dariusz-majchrzak/Meritum-1/docs/scans/1/cpu-mem.png

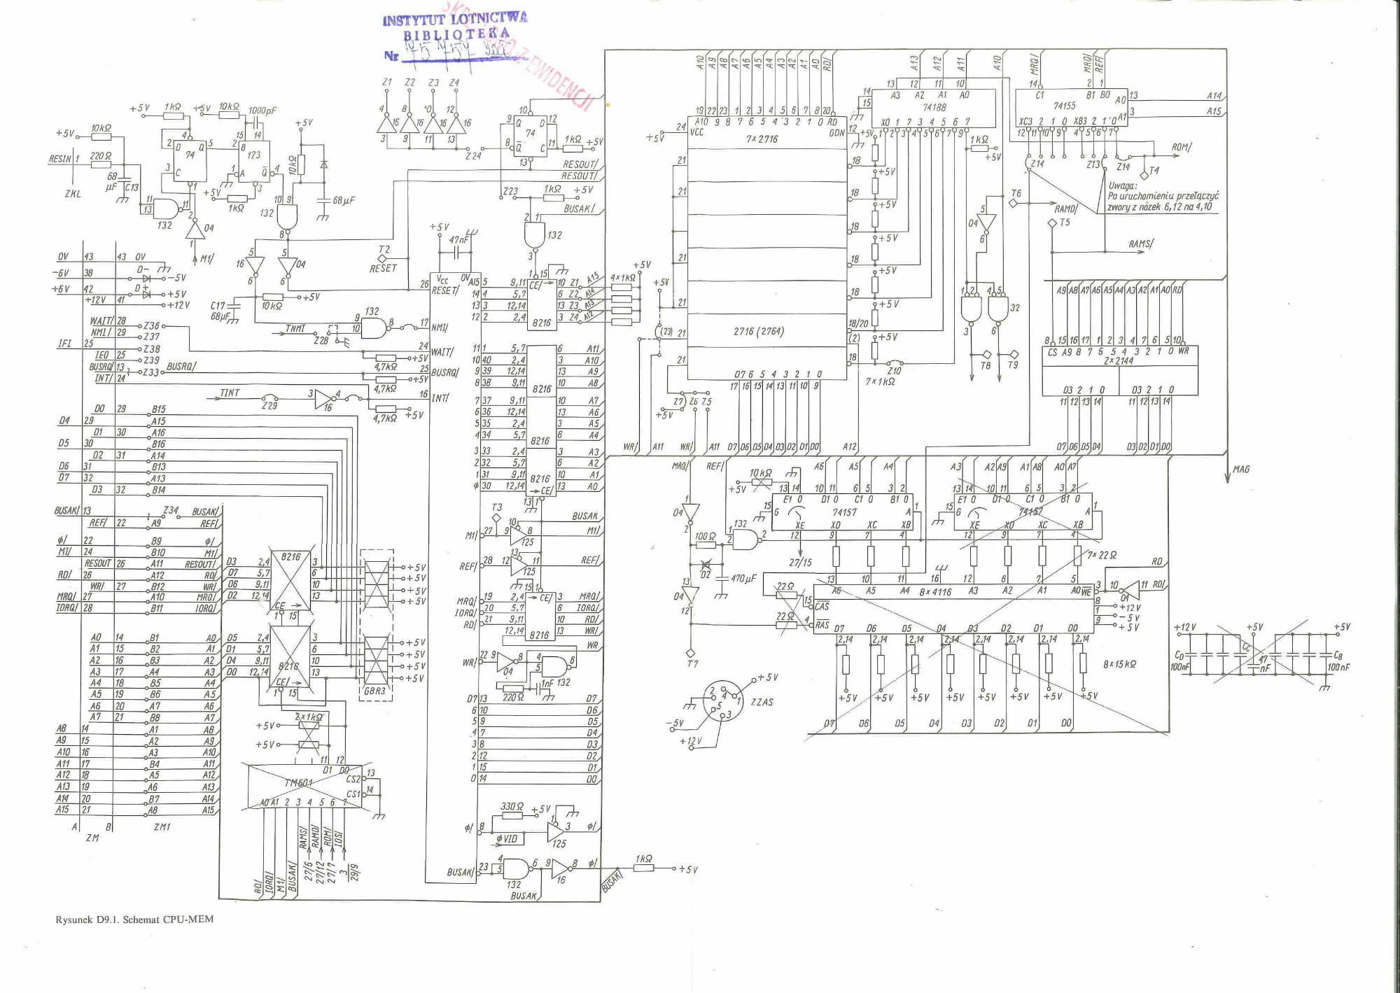
docs/scans/1/cpu-mem.png
