dariusz-majchrzak/Meritum-1/docs/scans/1/keyboard-1.png

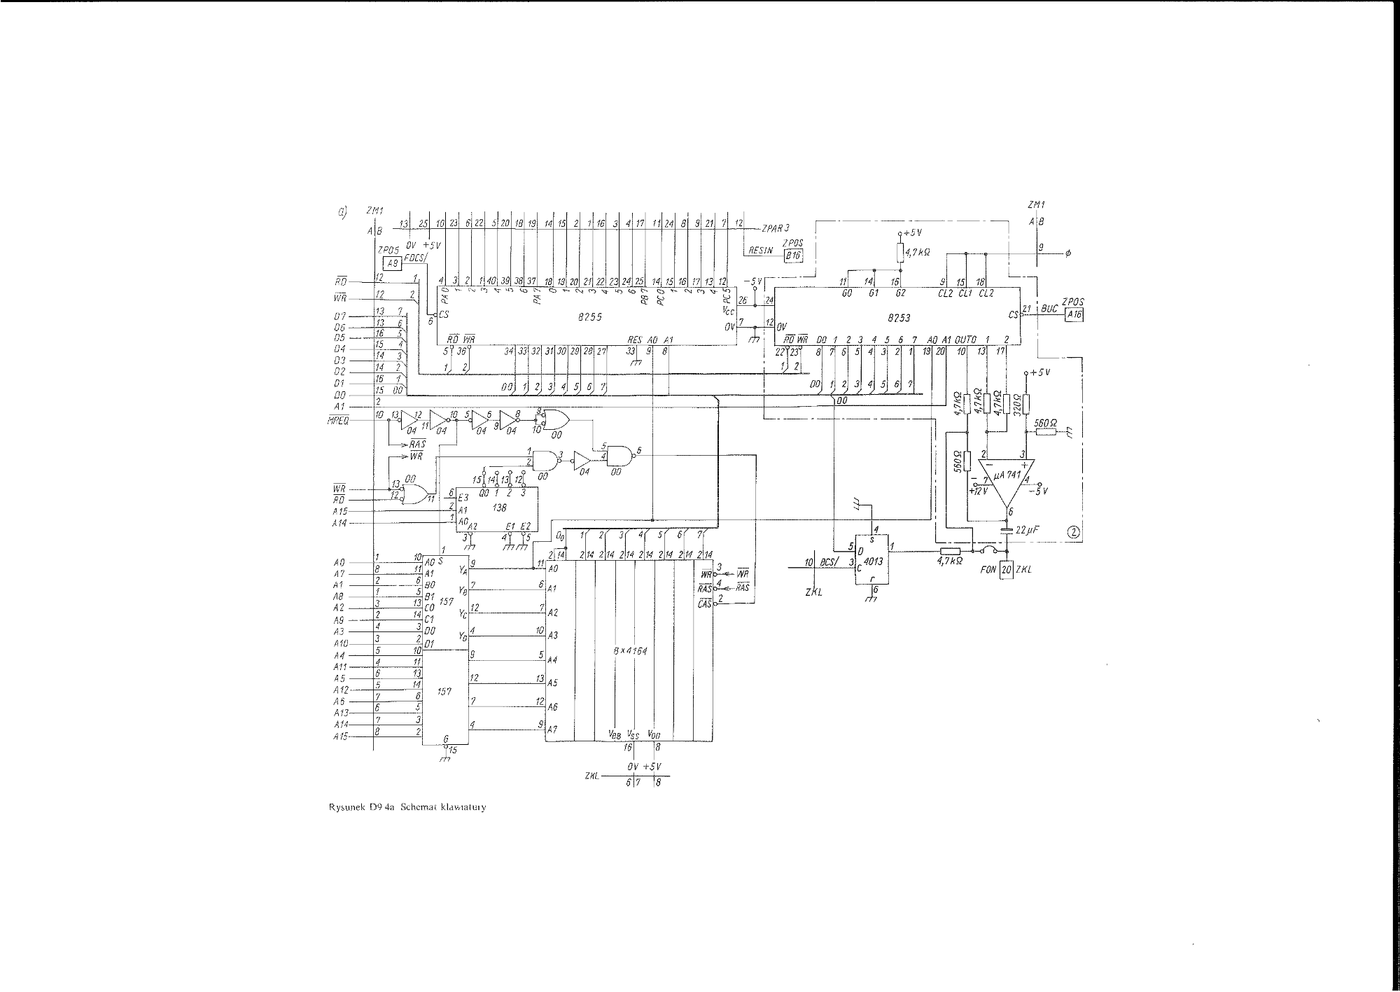
docs/scans/1/keyboard-1.png
