dariusz-majchrzak/Meritum-1/docs/scans/1/keyboard-2.png

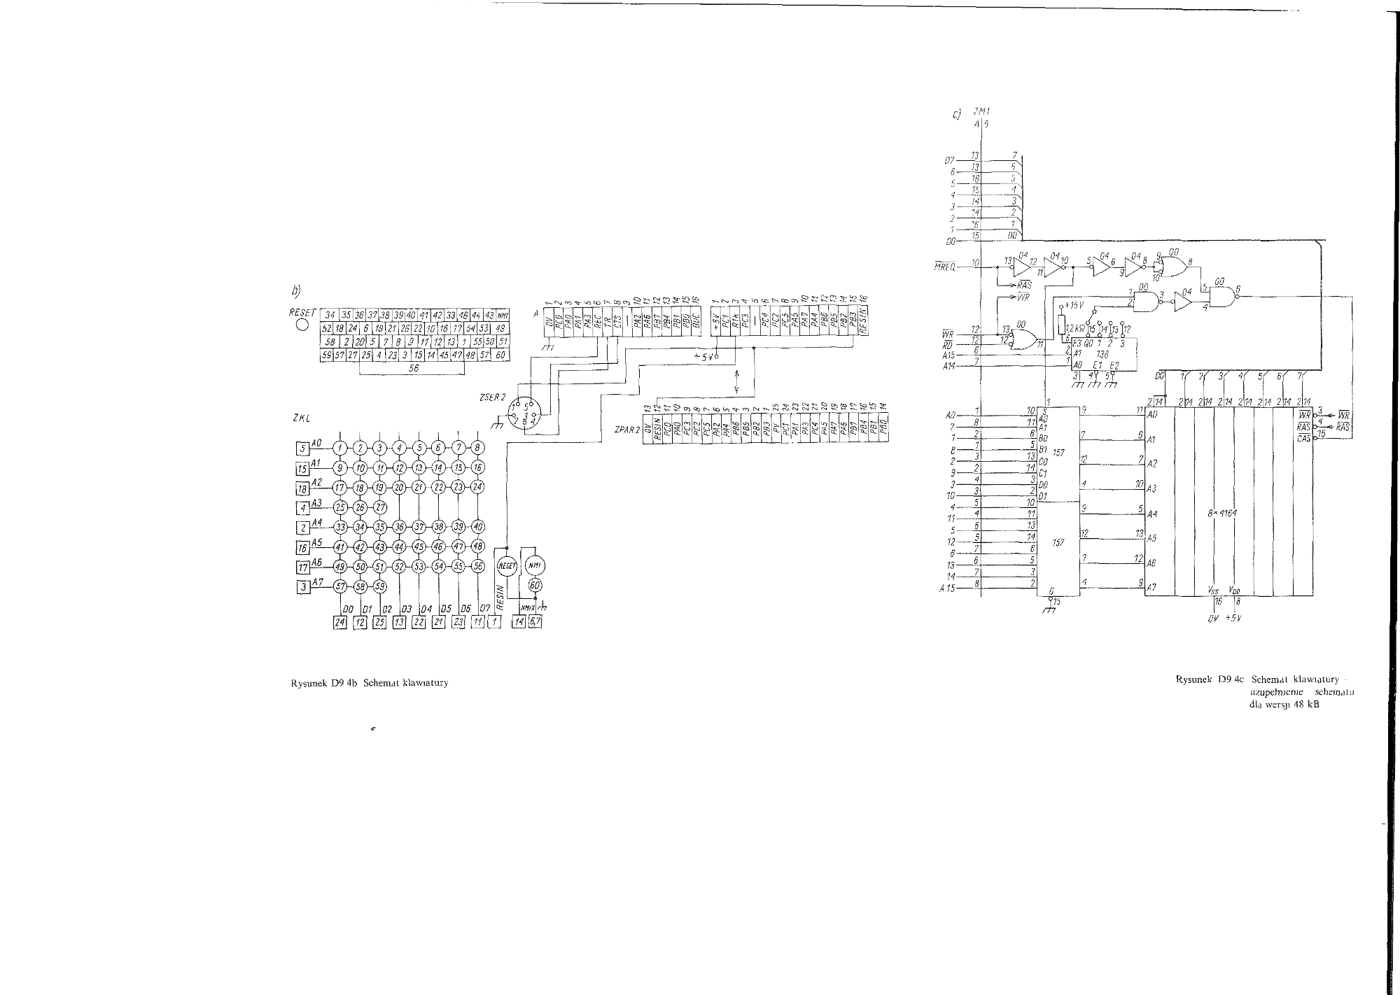
docs/scans/1/keyboard-2.png
