dariusz-majchrzak/Meritum-1/docs/scans/2/001.jpg

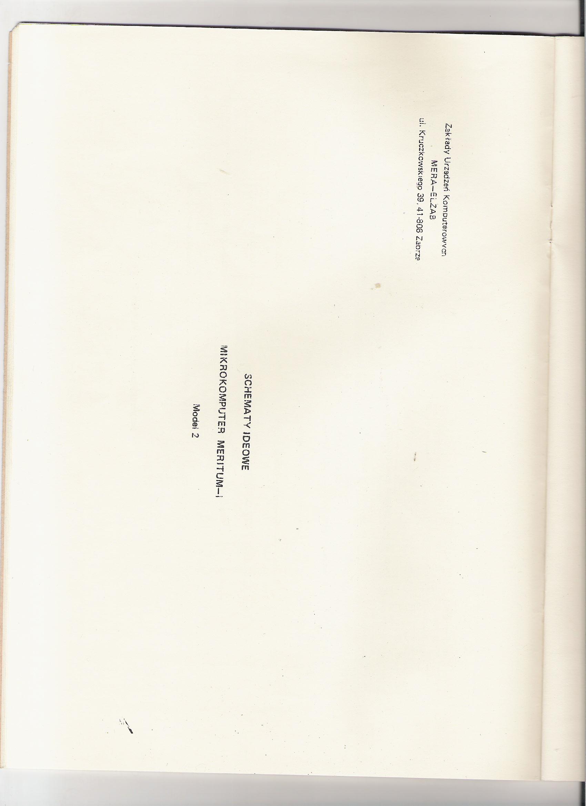
docs/scans/2/001.jpg
