dariusz-majchrzak/Meritum-1/docs/scans/2/002.jpg

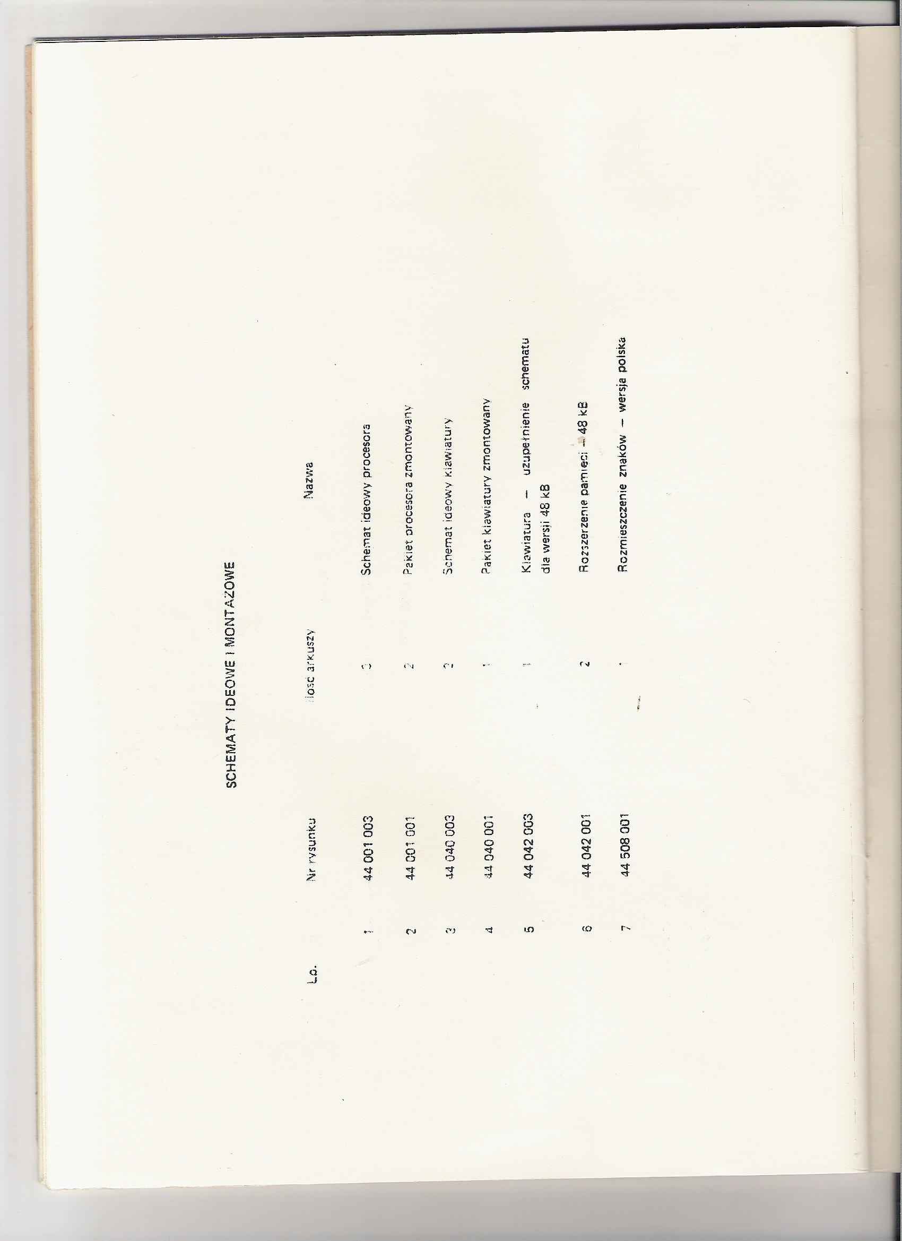
docs/scans/2/002.jpg
