dariusz-majchrzak/Meritum-1/docs/scans/2/003.jpg

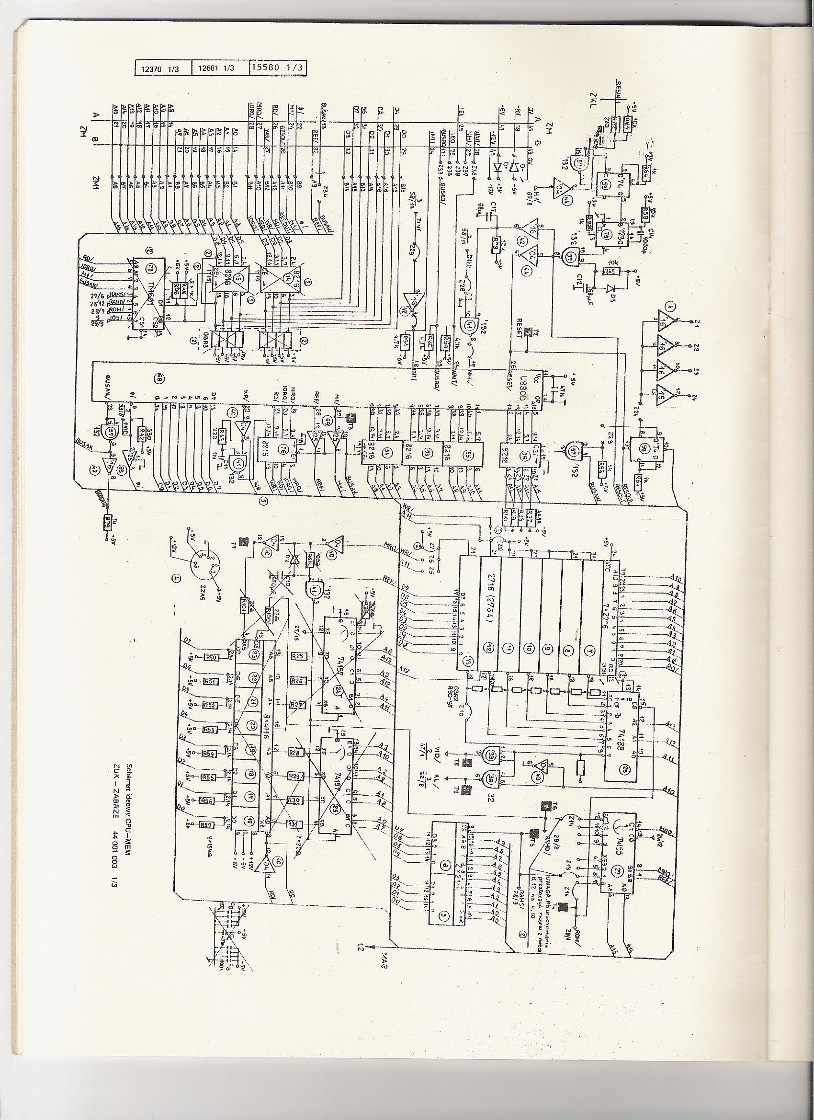
docs/scans/2/003.jpg
