dariusz-majchrzak/Meritum-1/docs/scans/2/004.jpg

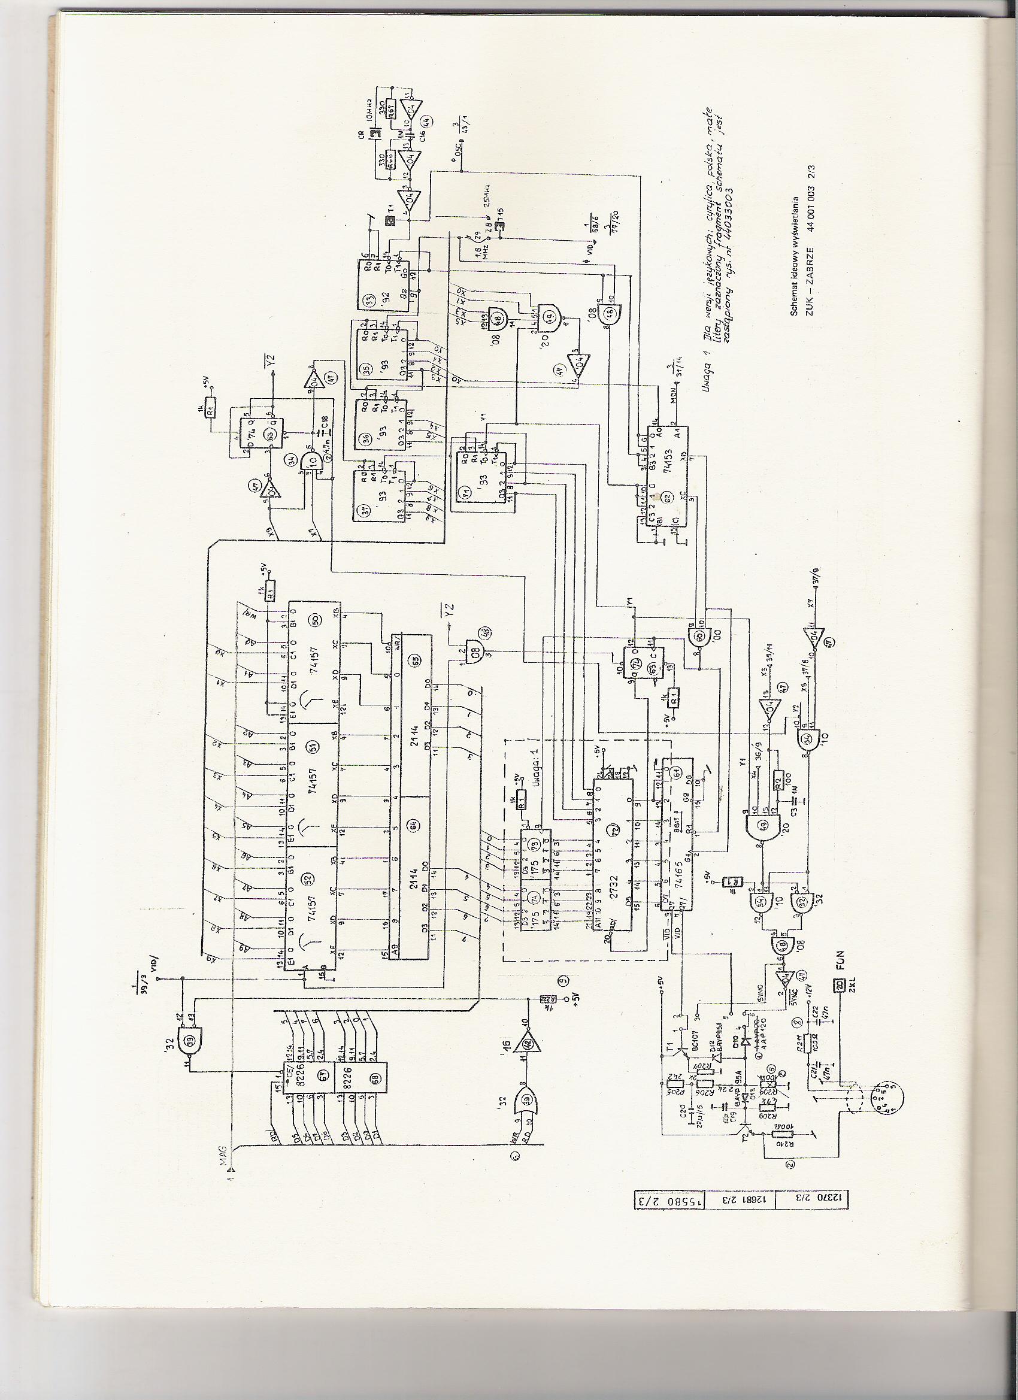
docs/scans/2/004.jpg
