dariusz-majchrzak/Meritum-1/docs/scans/2/005.jpg

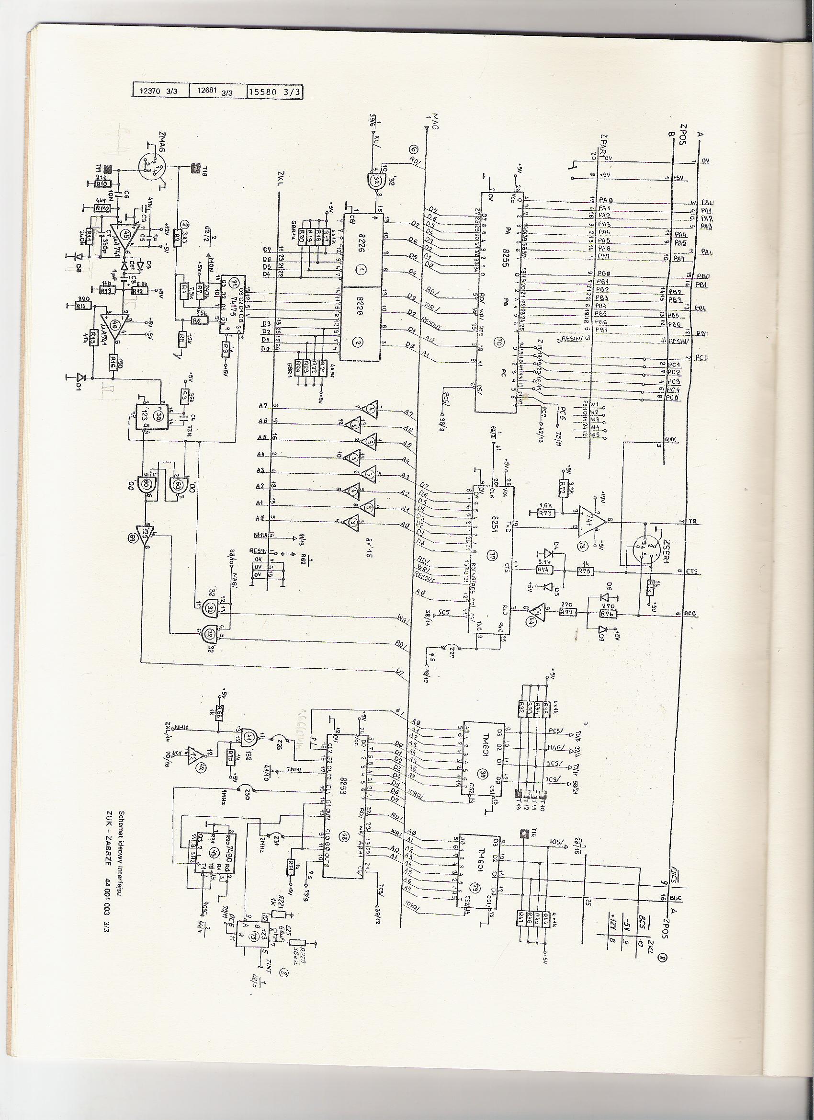
docs/scans/2/005.jpg
