dariusz-majchrzak/Meritum-1/docs/scans/2/006.jpg

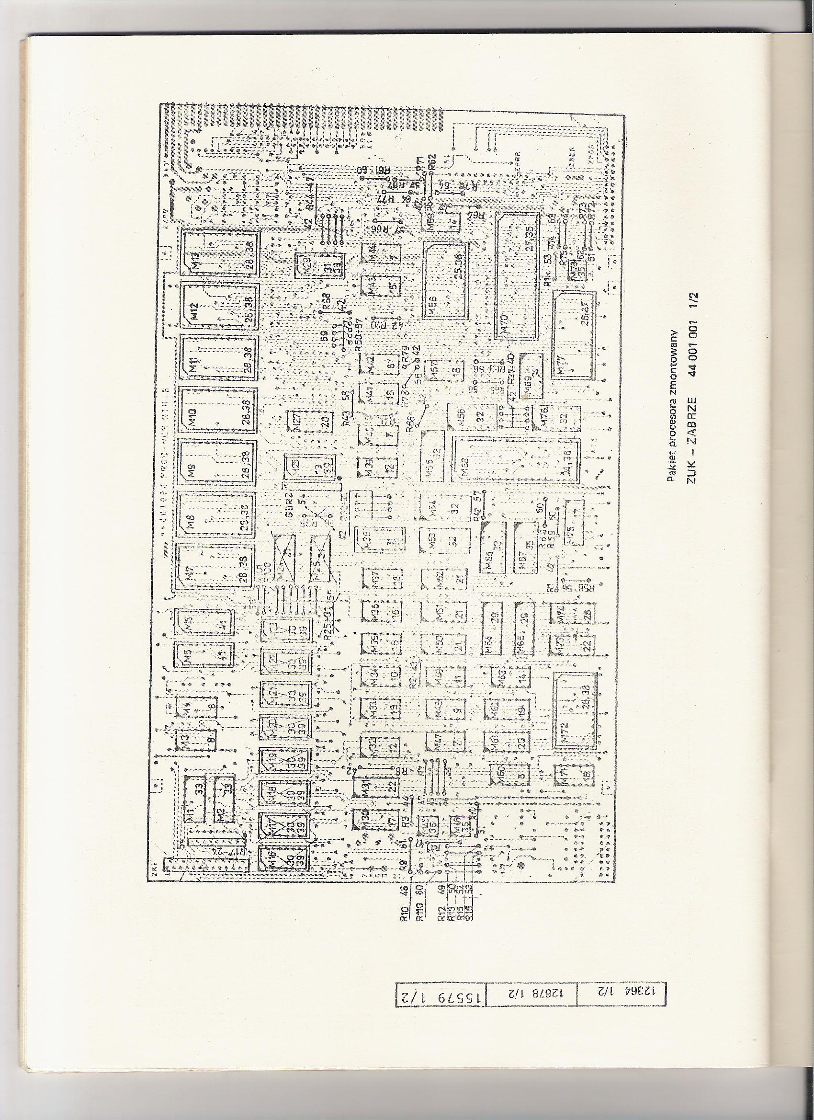
docs/scans/2/006.jpg
