dariusz-majchrzak/Meritum-1/docs/scans/2/007.jpg

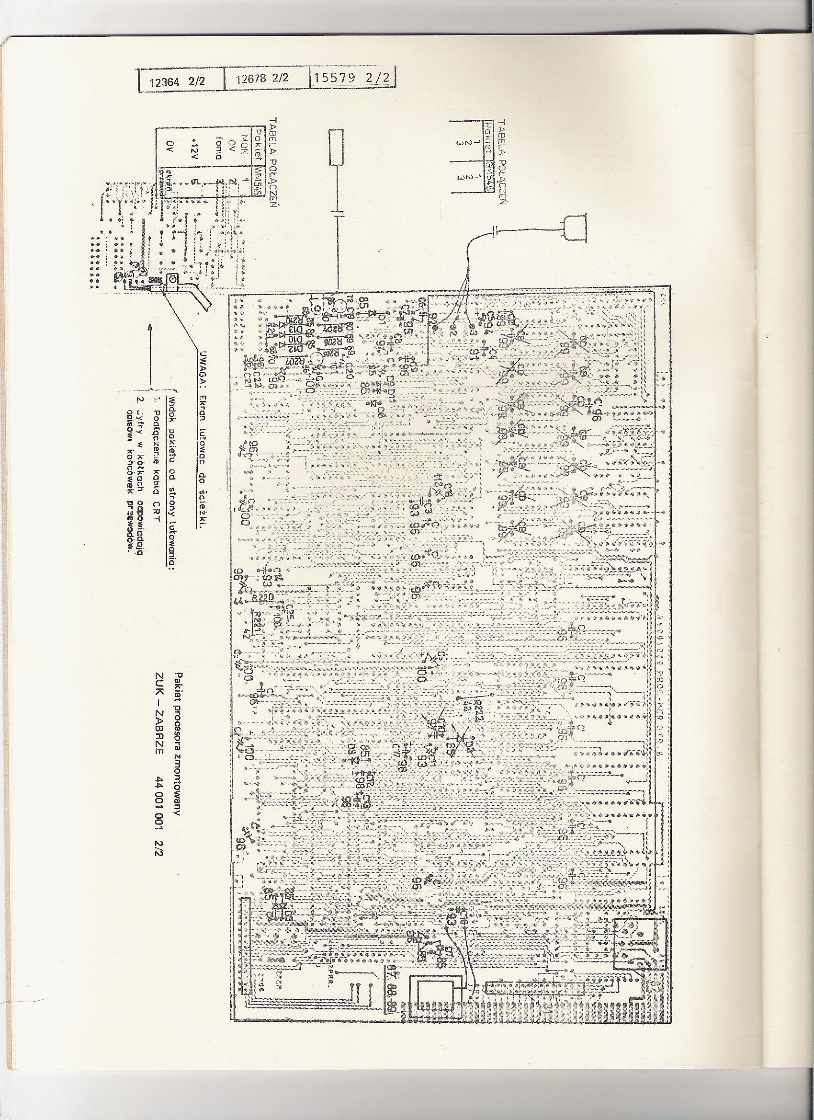
docs/scans/2/007.jpg
