dariusz-majchrzak/Meritum-1/docs/scans/2/008.jpg

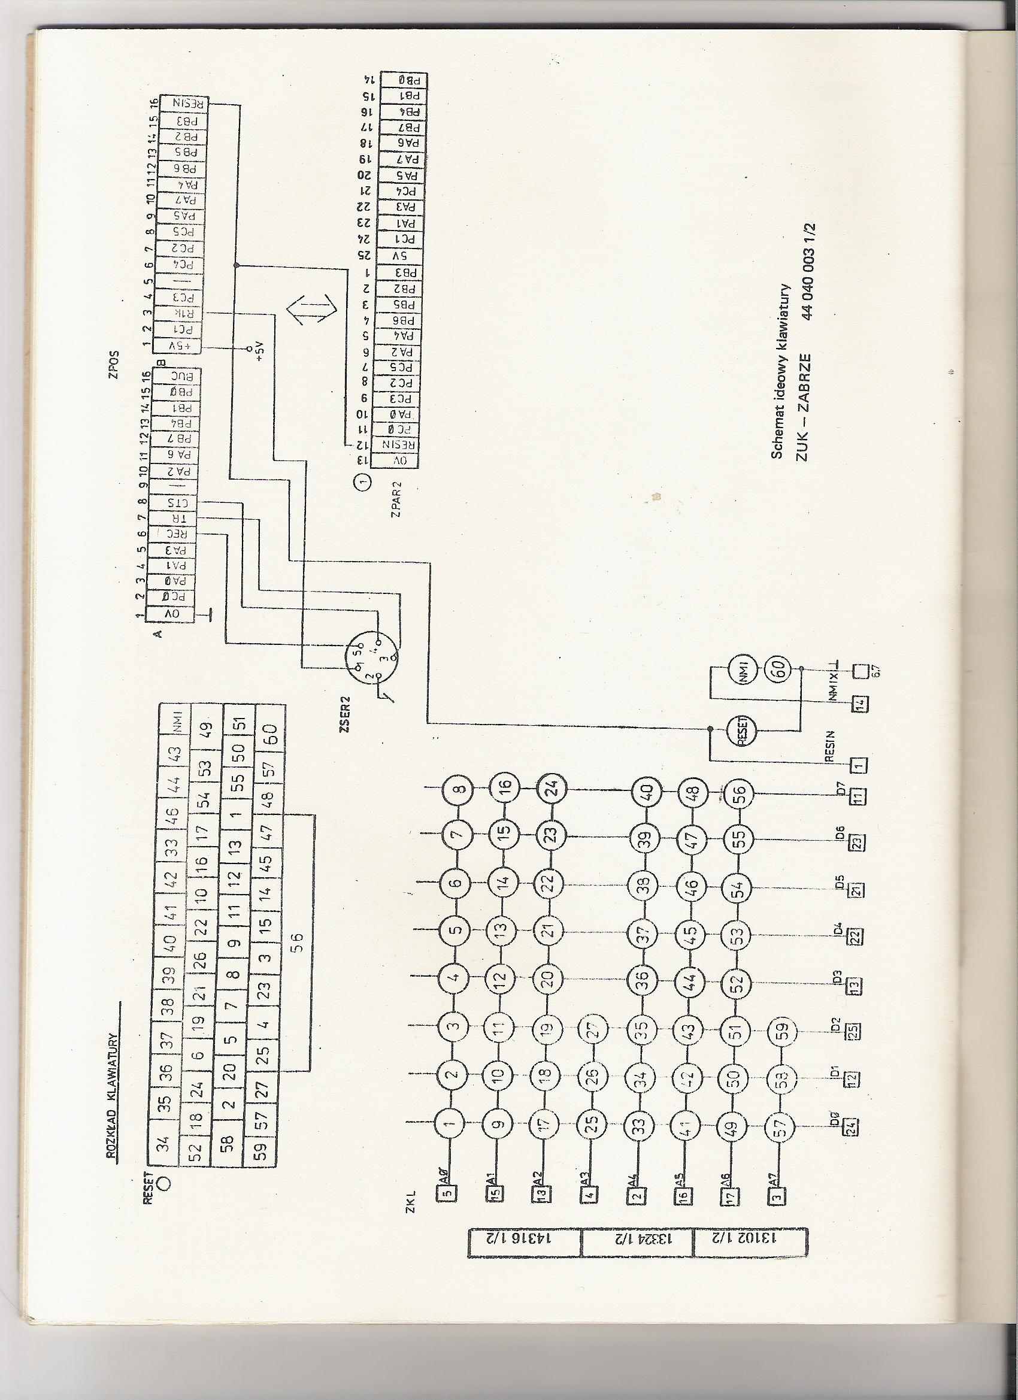
docs/scans/2/008.jpg
