dariusz-majchrzak/Meritum-1/docs/scans/2/009.jpg

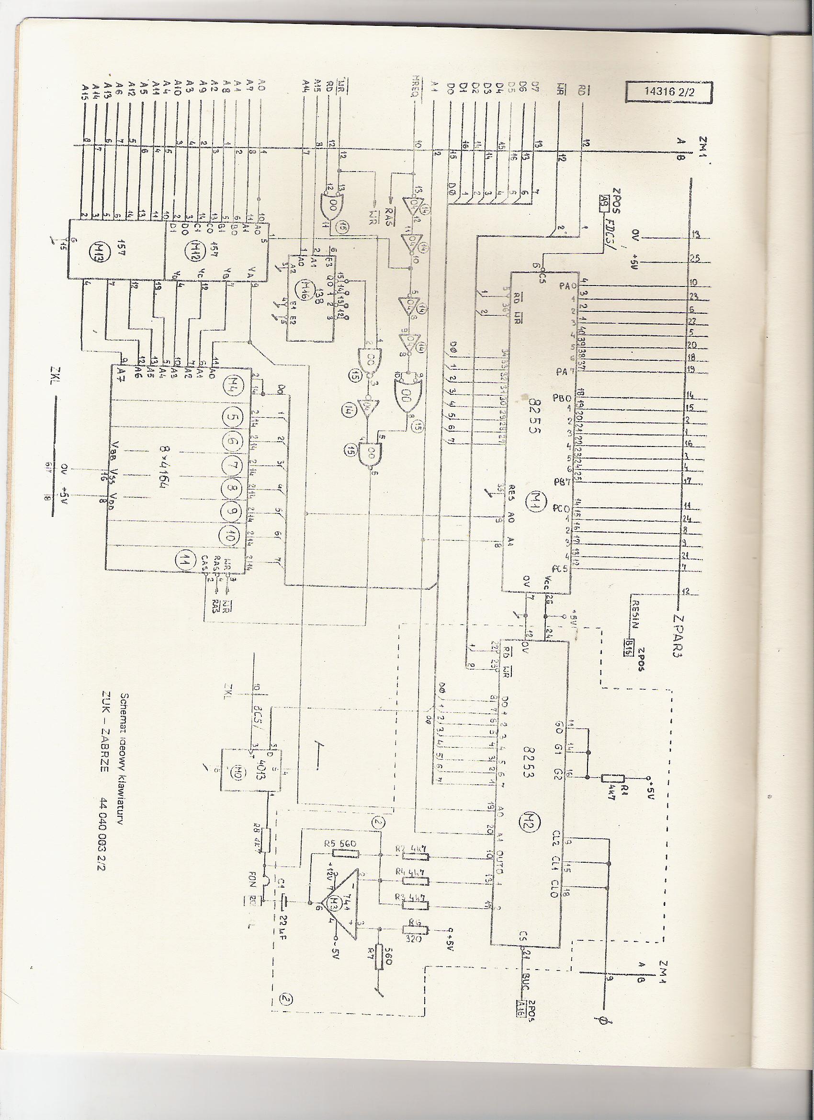
docs/scans/2/009.jpg
