dariusz-majchrzak/Meritum-1/docs/scans/2/010.jpg

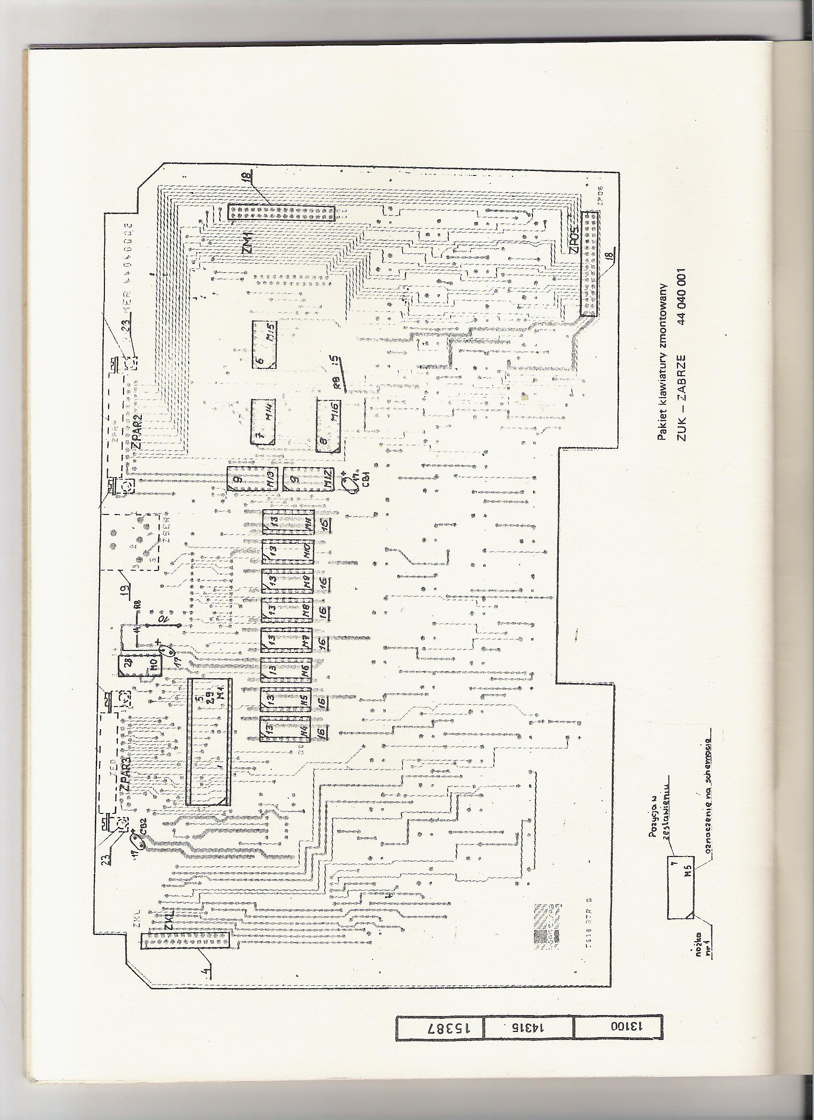
docs/scans/2/010.jpg
