dariusz-majchrzak/Meritum-1/docs/scans/2/011.jpg

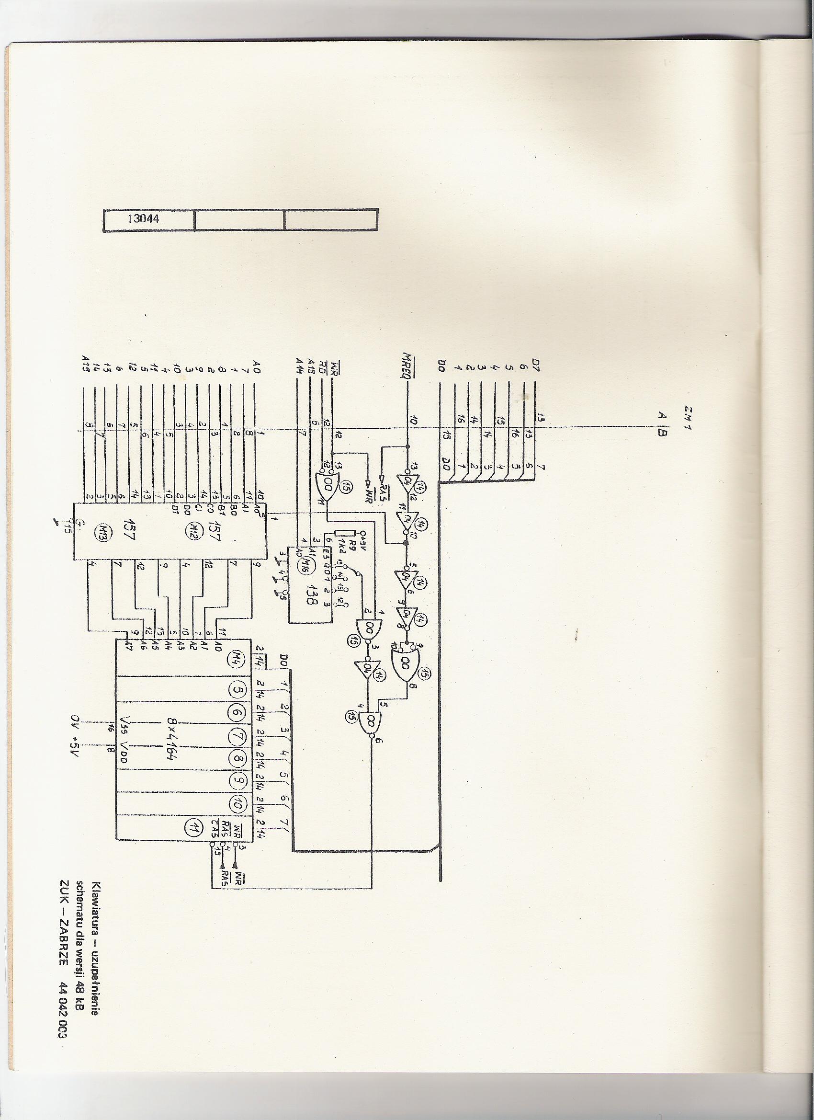
docs/scans/2/011.jpg
