dariusz-majchrzak/Meritum-1/docs/scans/2/012.jpg

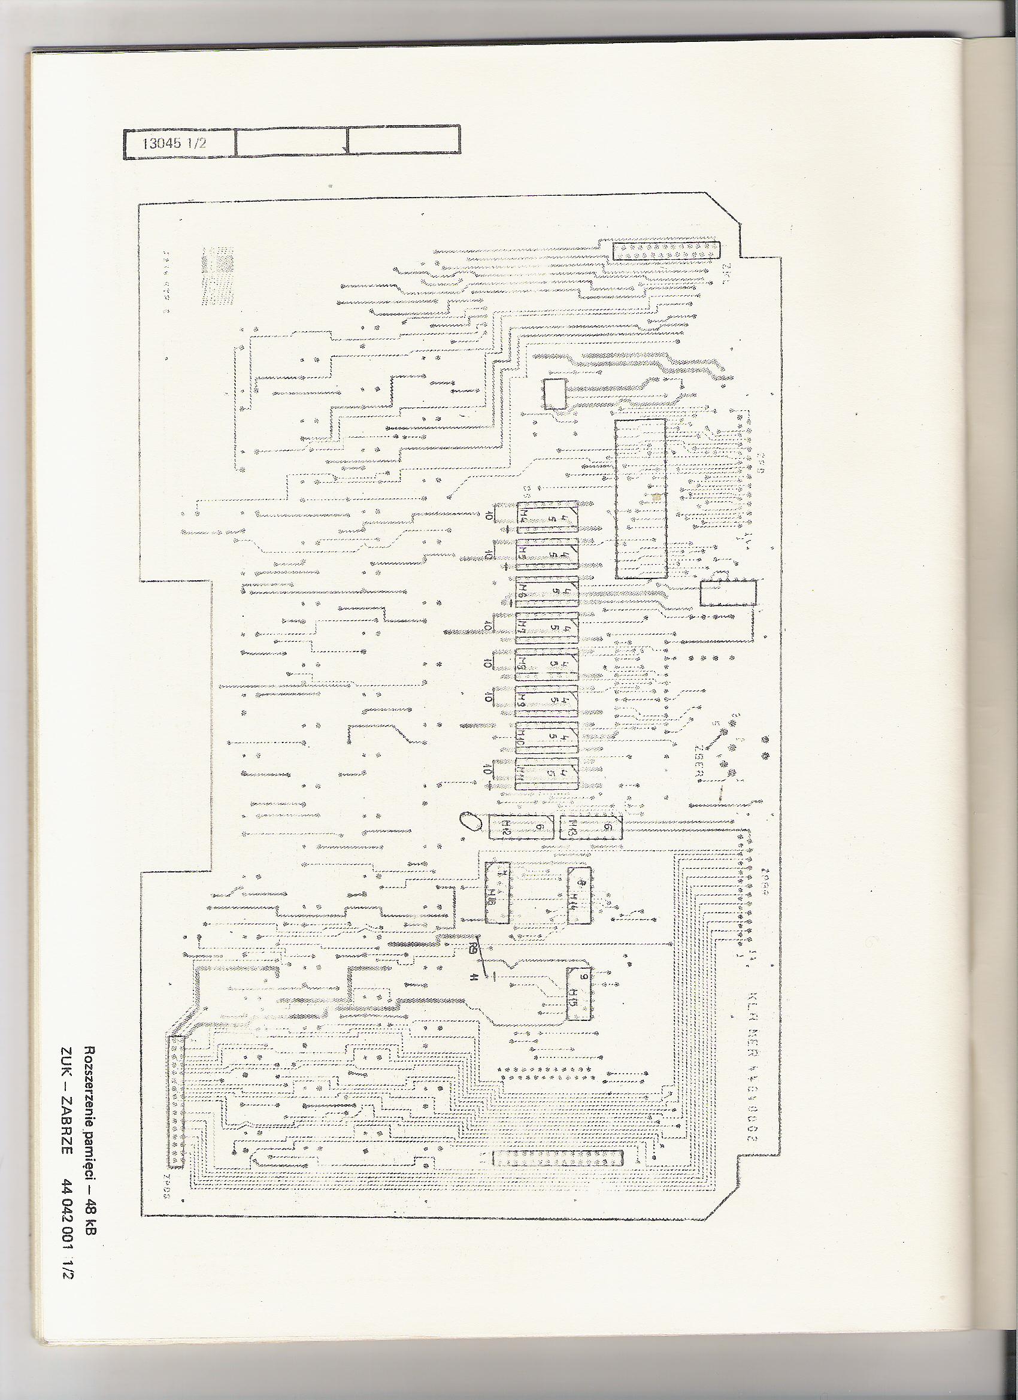
docs/scans/2/012.jpg
