dariusz-majchrzak/Meritum-1/docs/scans/2/013.jpg

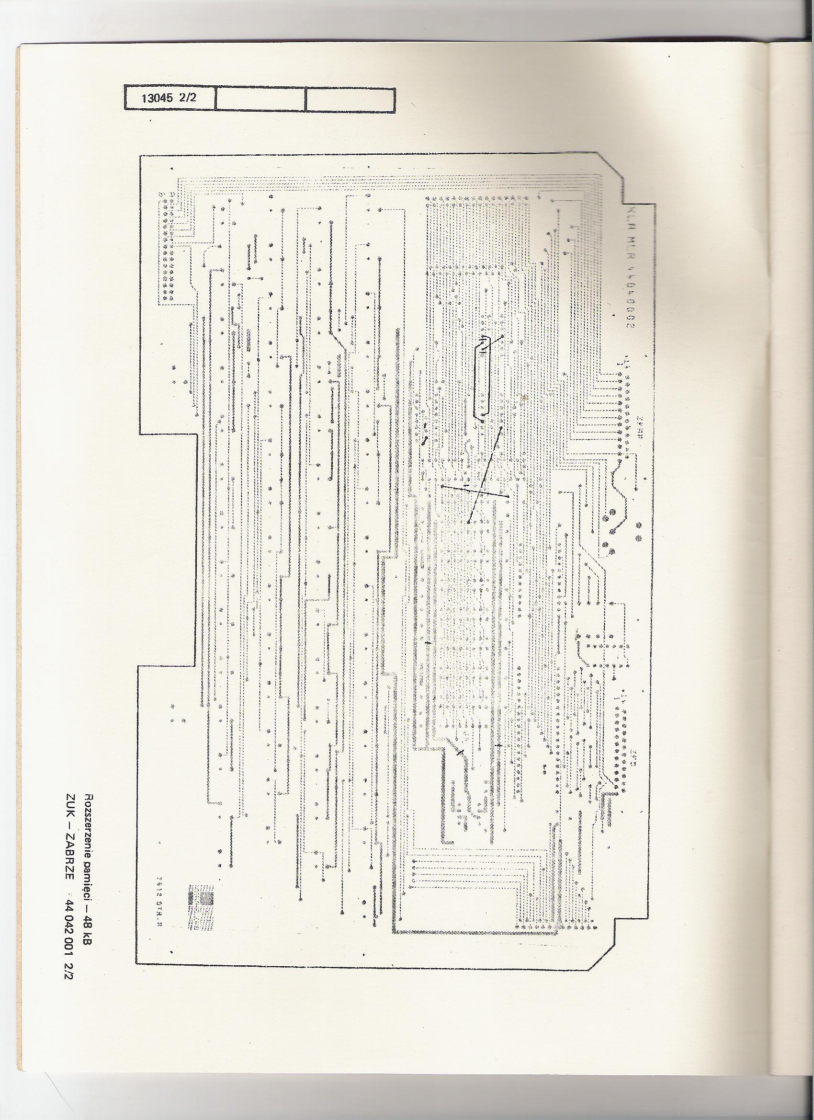
docs/scans/2/013.jpg
