dariusz-majchrzak/Meritum-1/docs/scans/2/014.jpg

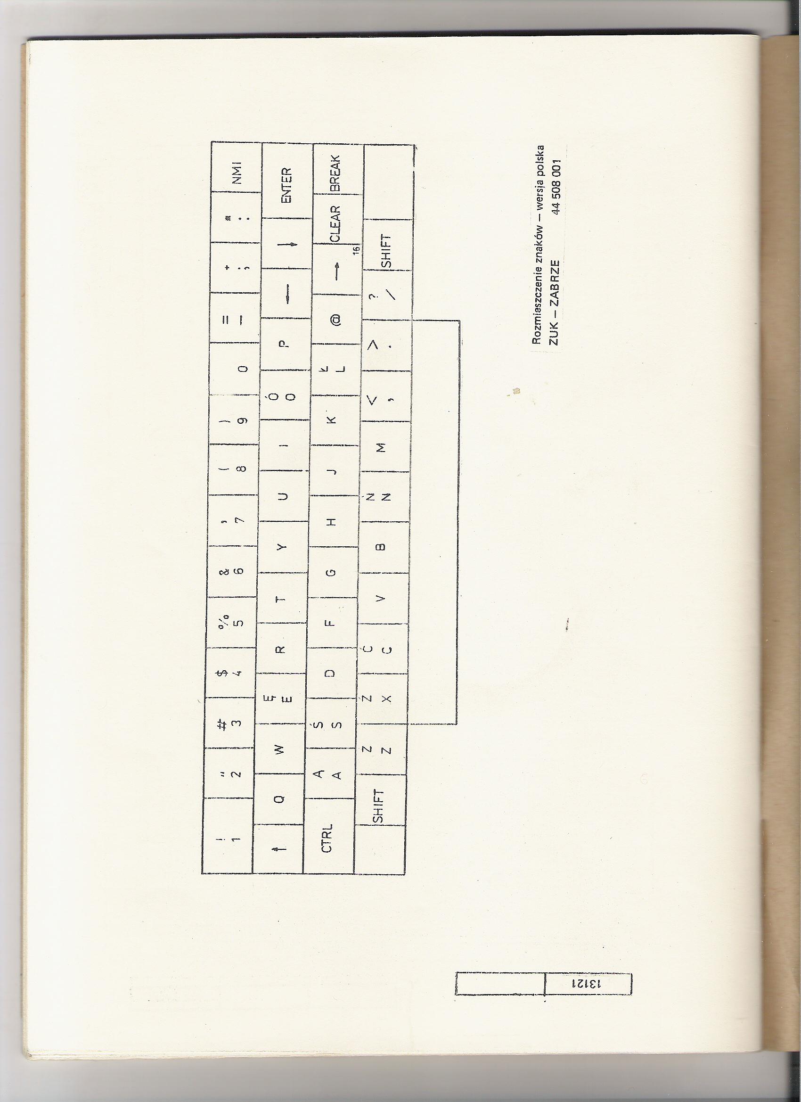
docs/scans/2/014.jpg
