dariusz-majchrzak/Meritum-1/docs/scans/3/D9-2.png

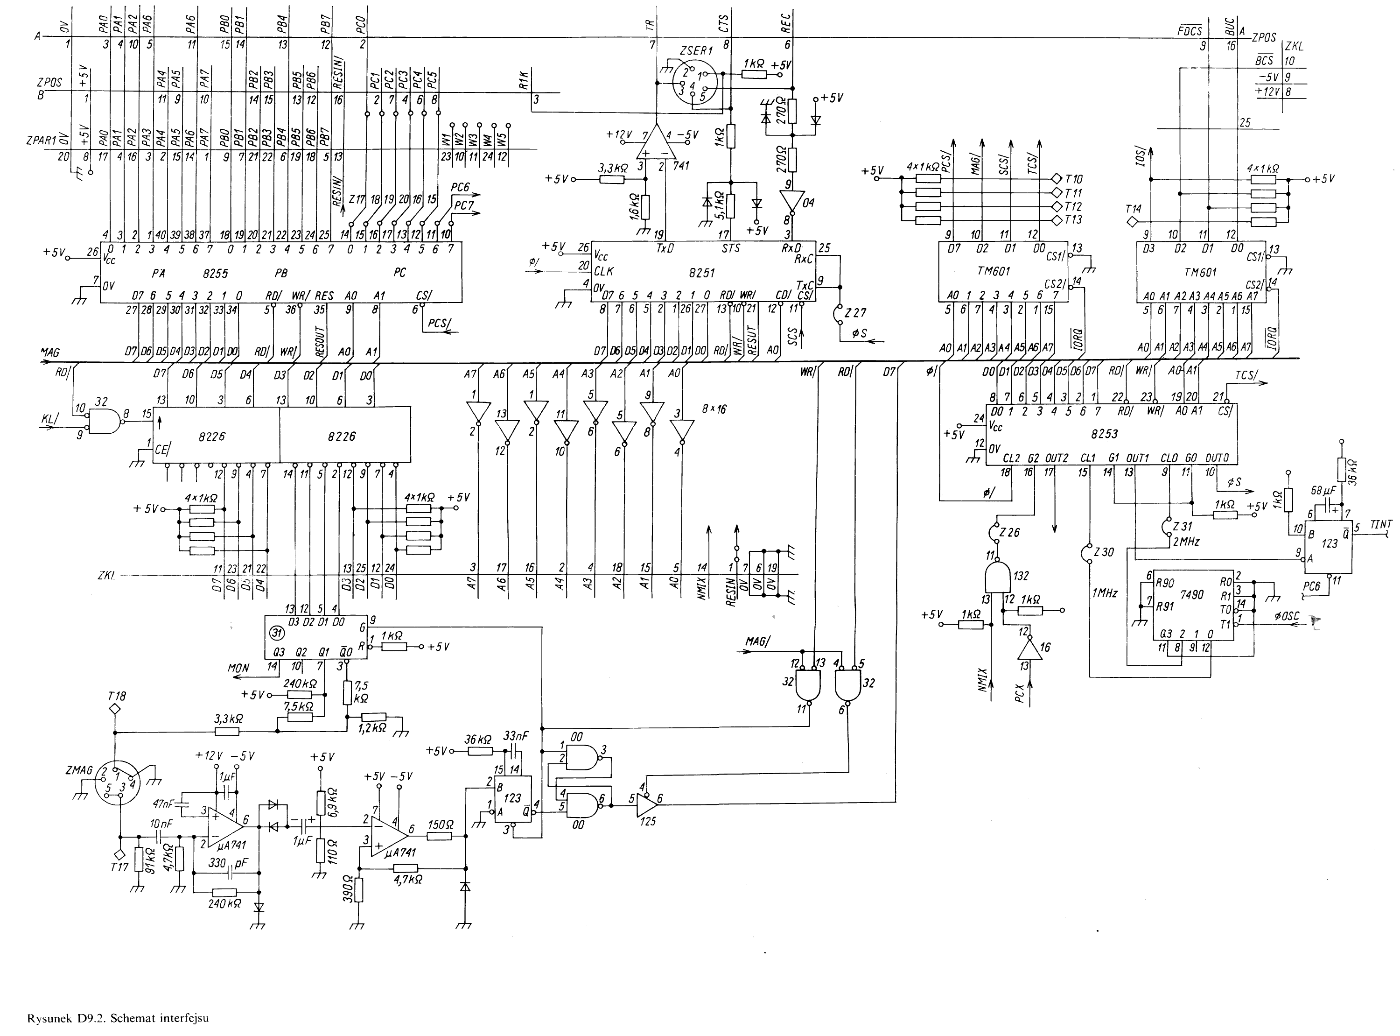
docs/scans/3/D9-2.png
