dariusz-majchrzak/Meritum-1/docs/scans/3/D9-3.png

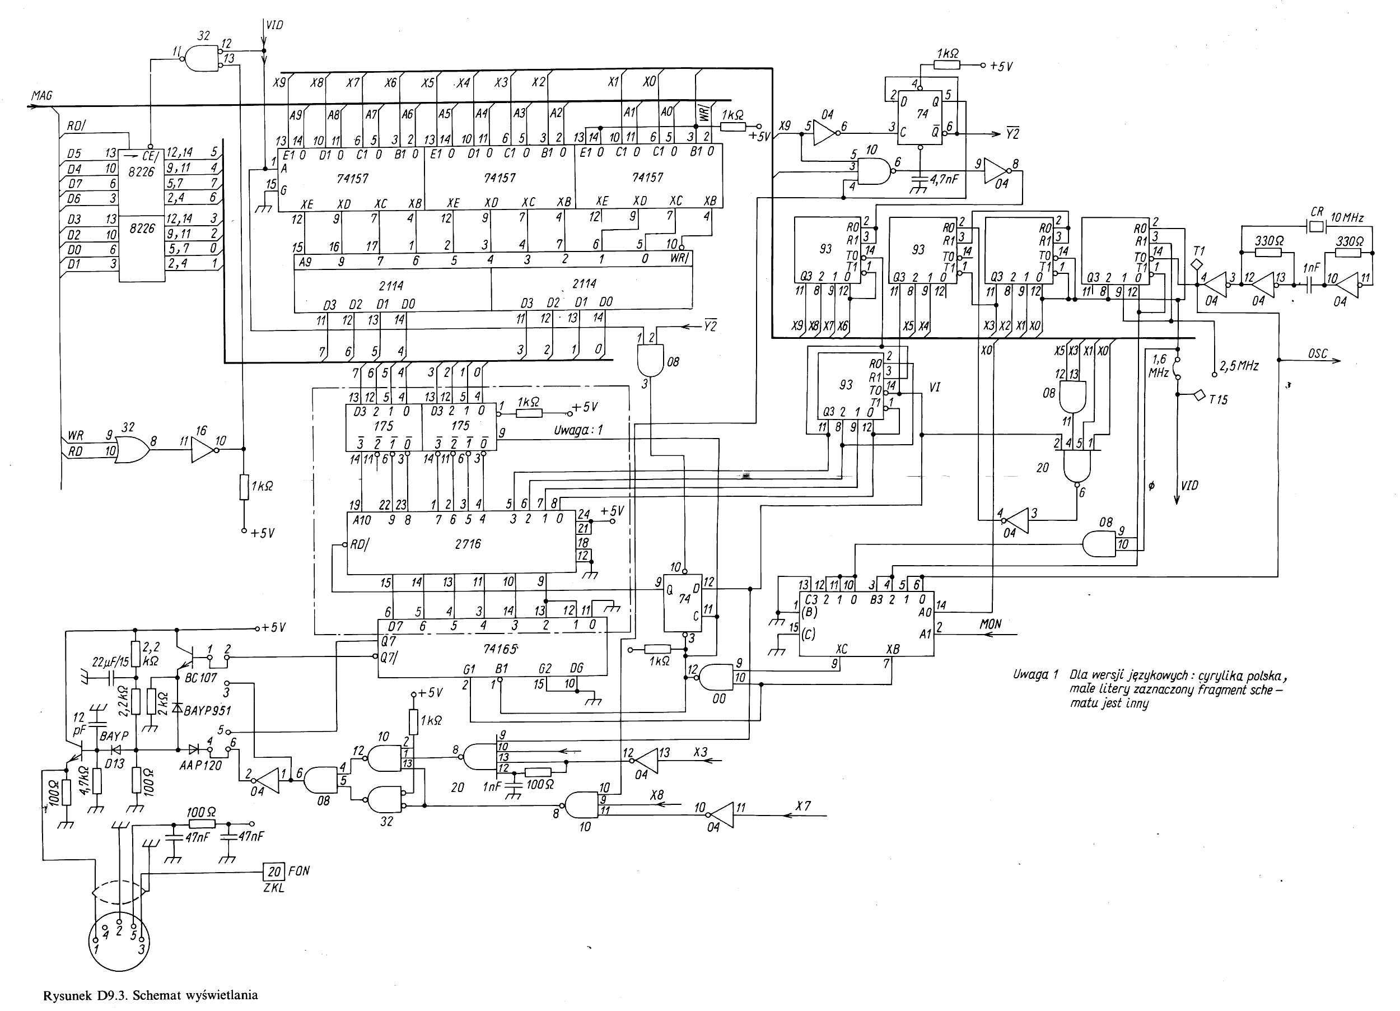
docs/scans/3/D9-3.png
