dariusz-majchrzak/Meritum-1/docs/scans/3/D9-4a.png

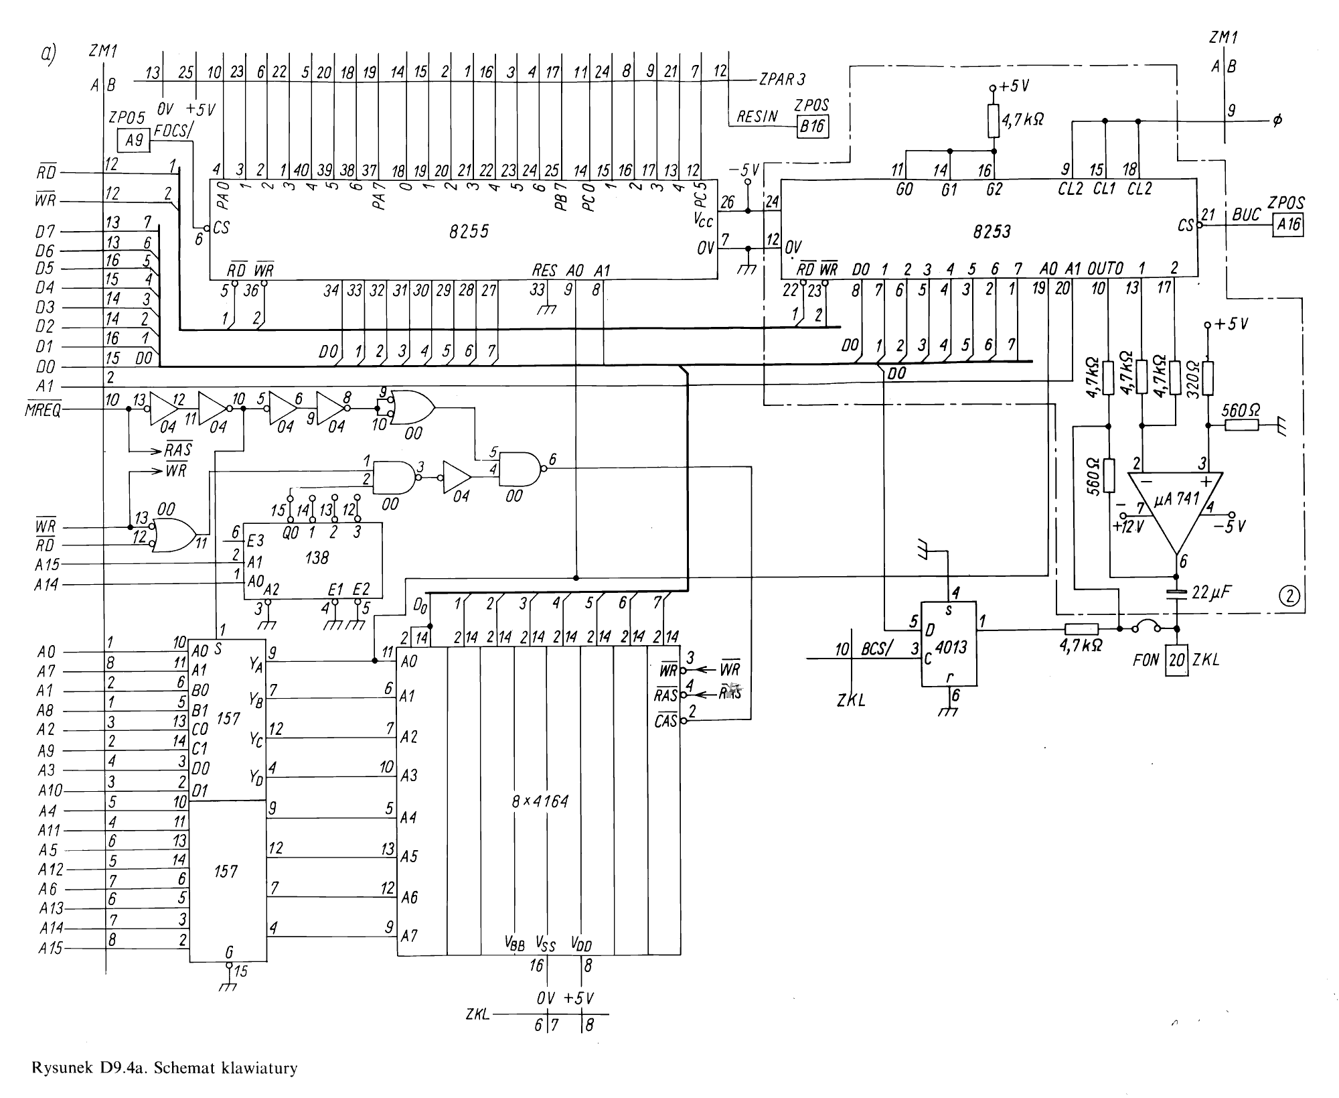
docs/scans/3/D9-4a.png
