dariusz-majchrzak/Meritum-1/docs/scans/3/D9-4b.png

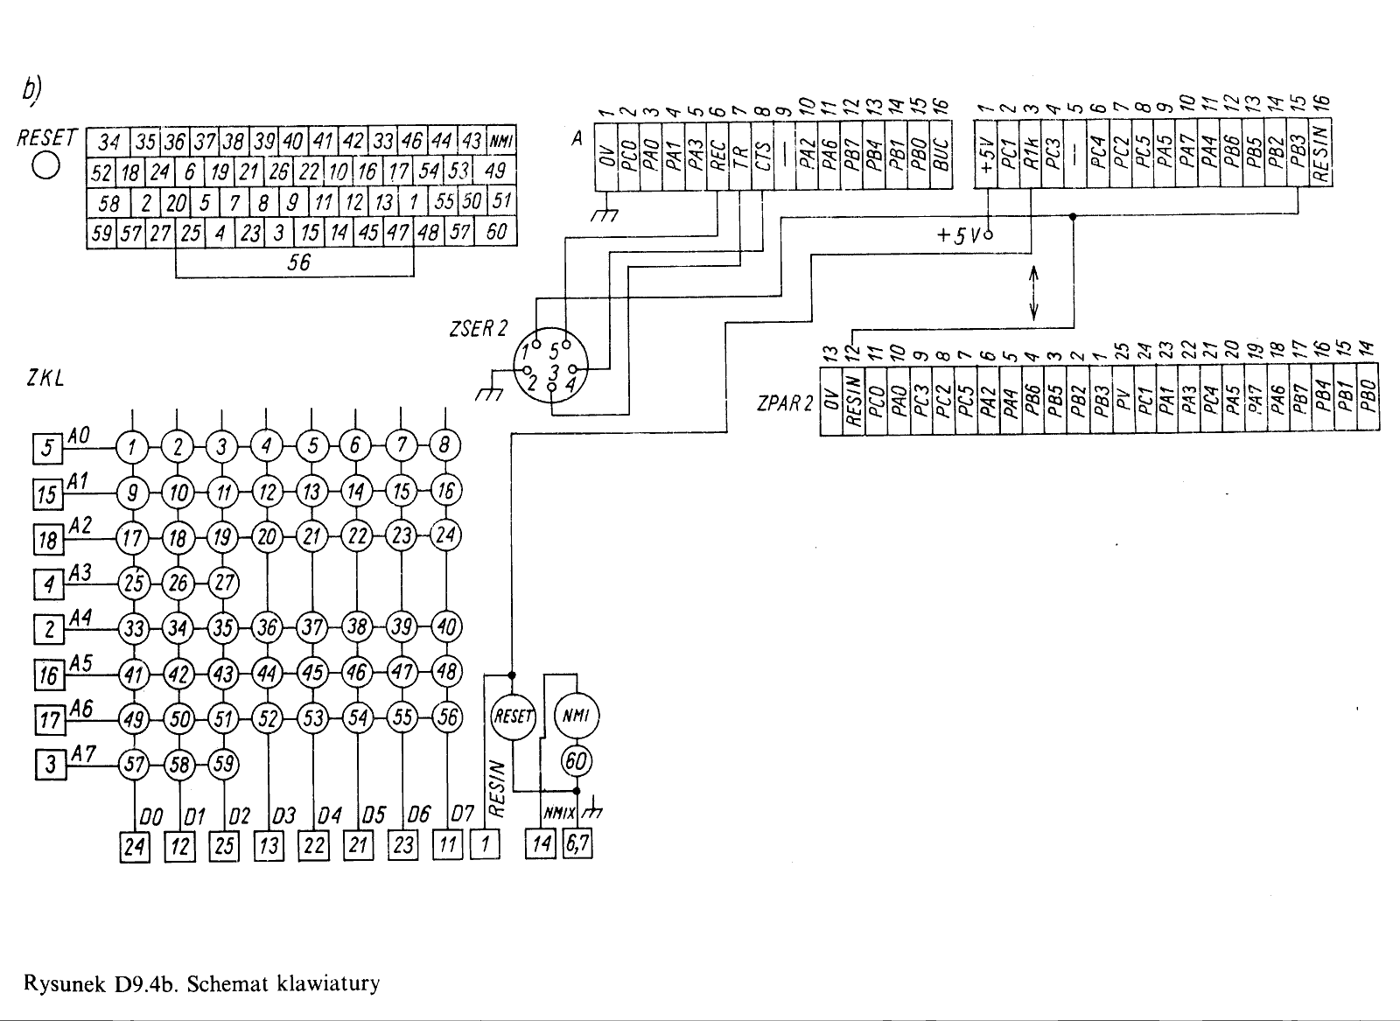
docs/scans/3/D9-4b.png
