dariusz-majchrzak/Meritum-1/Meritum_KLT/img/Meritum1_KLT_BOTTOM.png

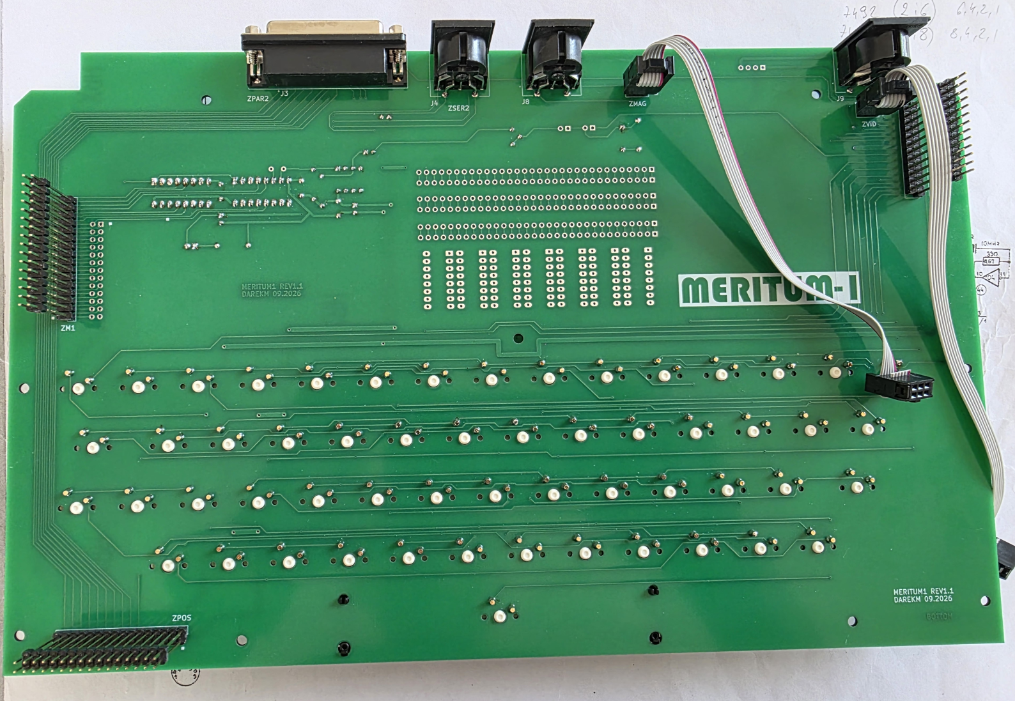
Meritum_KLT/img/Meritum1_KLT_BOTTOM.png
