dariusz-majchrzak/Meritum-1/Meritum_KLT/img/Meritum1_KLT_PCB_TOP.png

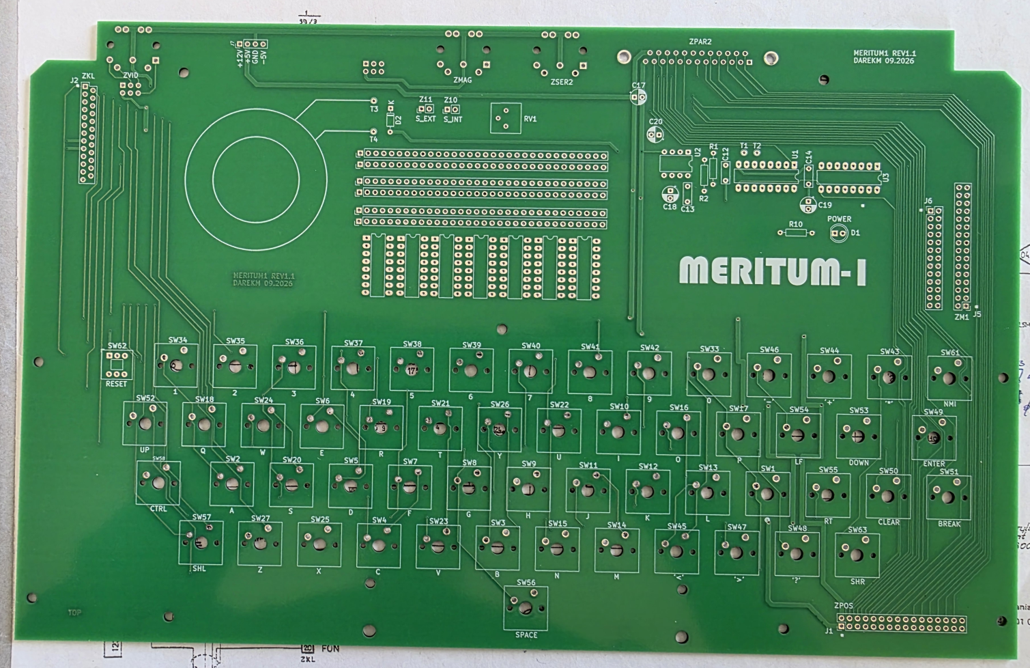
Meritum_KLT/img/Meritum1_KLT_PCB_TOP.png
