dariusz-majchrzak/Meritum-1/Meritum_PGW/img/Meritum1_PGW_BOTTOM.png

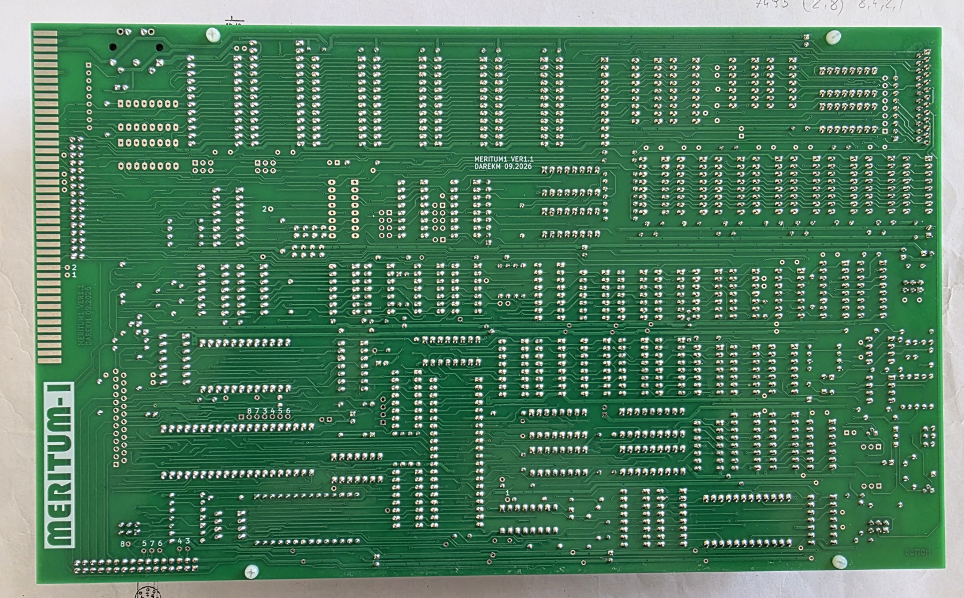
Meritum_PGW/img/Meritum1_PGW_BOTTOM.png
