dariusz-majchrzak/Meritum-1/Meritum_PGW/img/Meritum1_stack.png

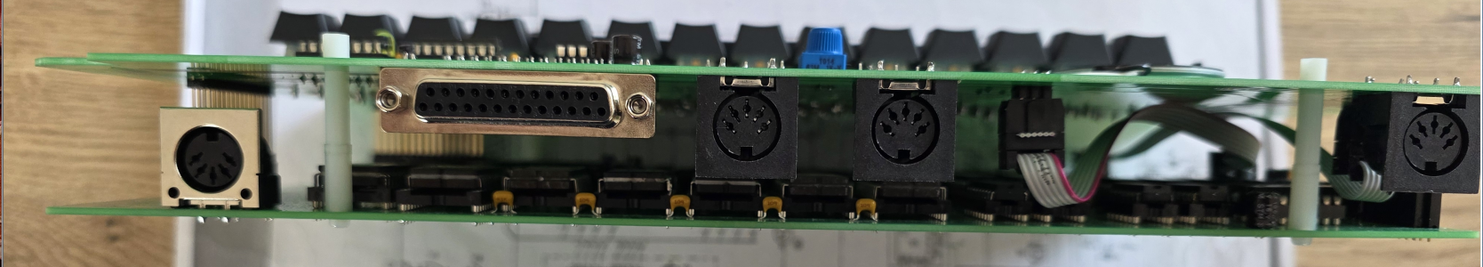
Meritum_PGW/img/Meritum1_stack.png
